IronMines/PDR2018/photo/Avancement du projet/IMG_1914.JPG

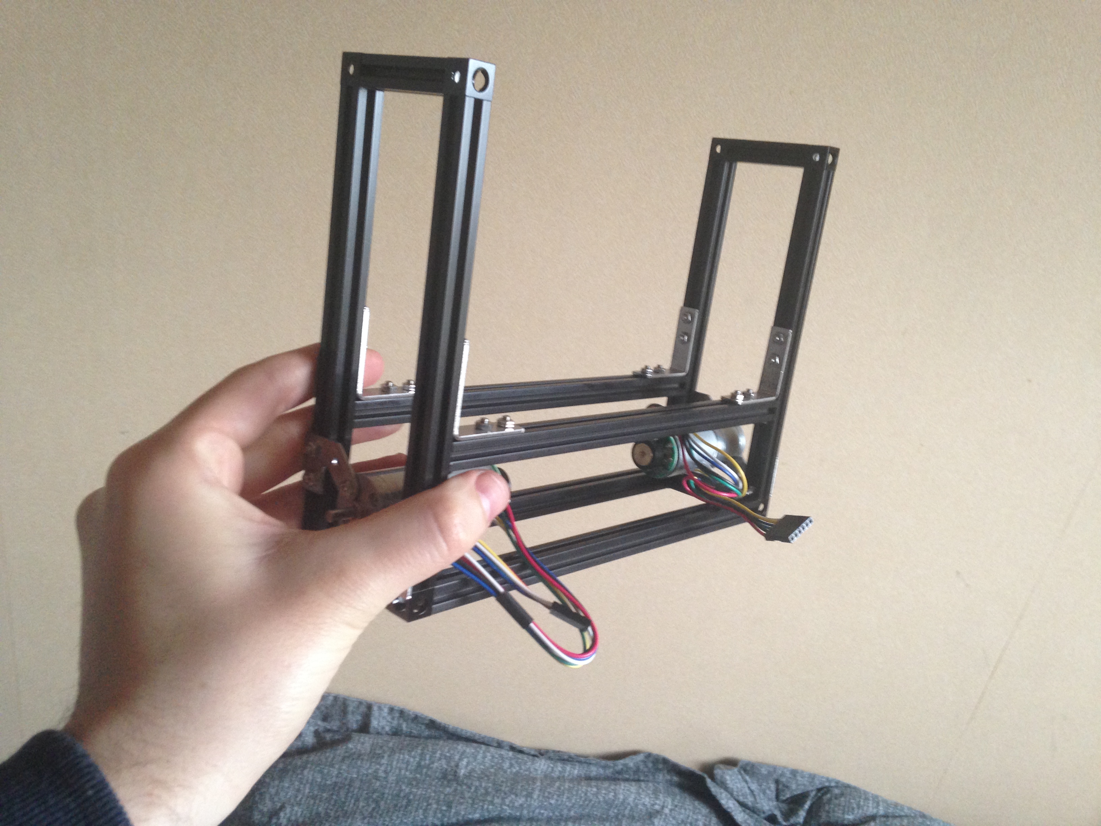
photo/Avancement du projet/IMG_1914.JPG
