IronMines/PDR2018/photo/Avancement du projet/IMG_1923.JPG

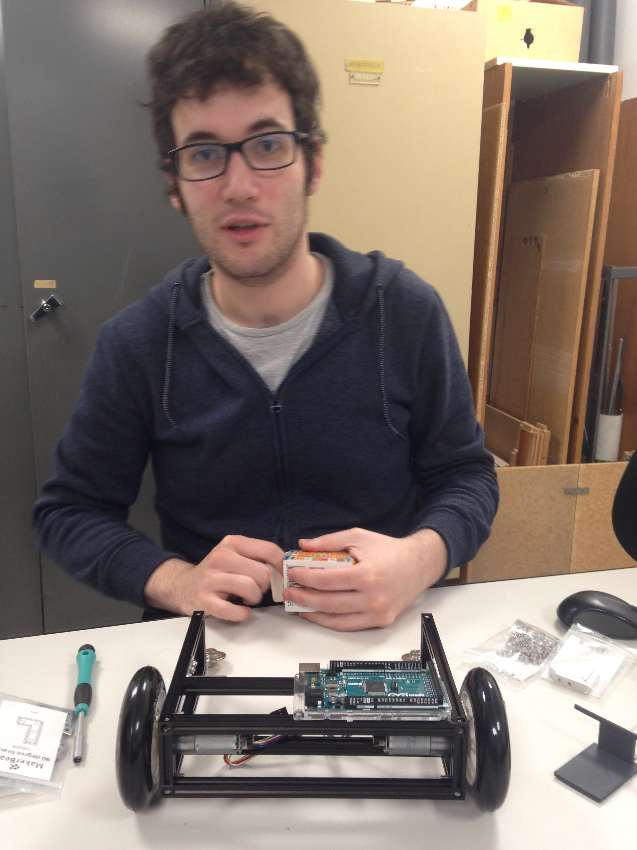
photo/Avancement du projet/IMG_1923.JPG
