IronMines/PDR2018/photo/Avancement du projet/IMG_1924.JPG

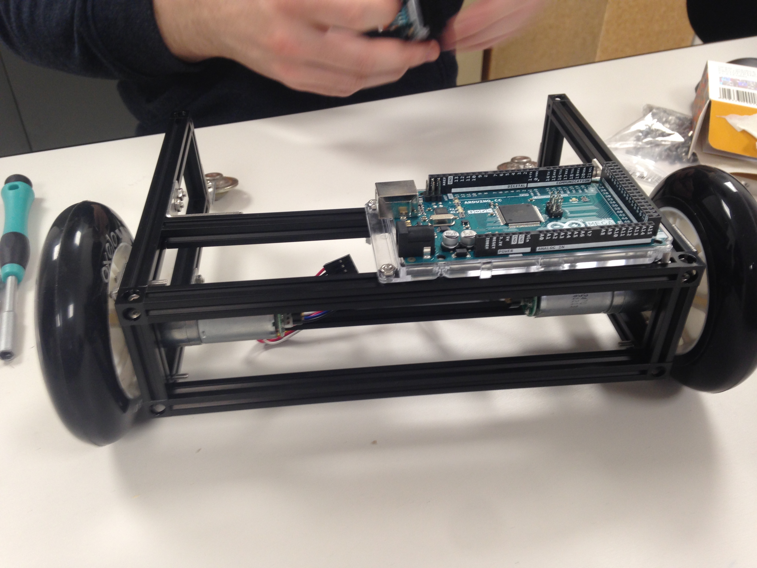
photo/Avancement du projet/IMG_1924.JPG
