IronMines/PDR2018/photo/Avancement du projet/IMG_1926.JPG

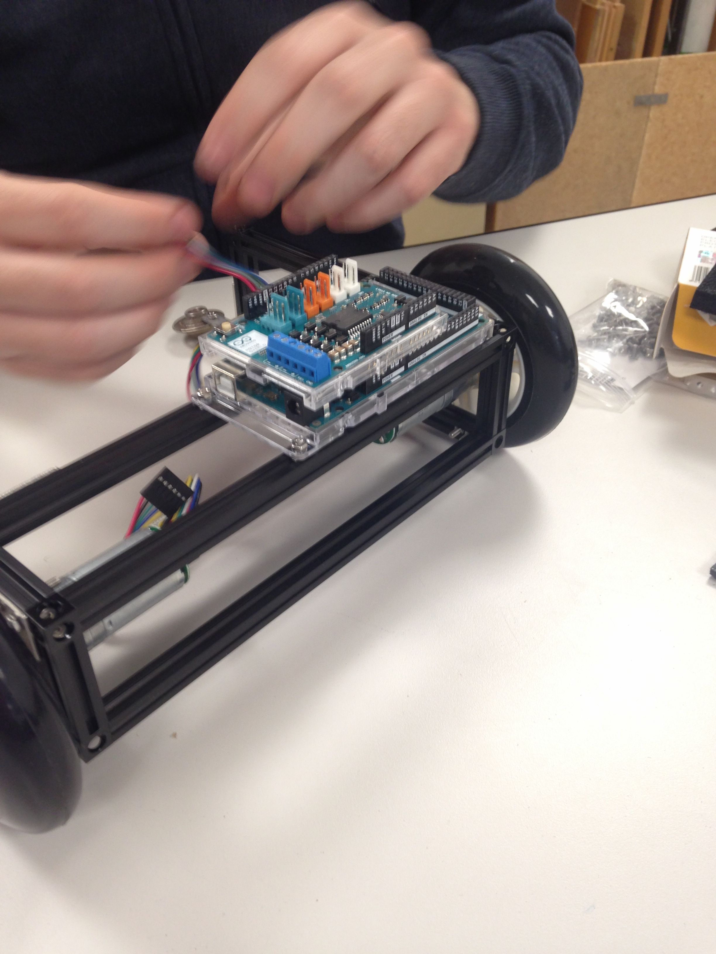
photo/Avancement du projet/IMG_1926.JPG
