IronMines/PDR2018/arduino/Sloeber/sloeber.ino.cpp

#ifdef __IN_ECLIPSE__
//This is a automatic generated file
//Please do not modify this file
//If you touch this file your change will be overwritten during the next build
//This file has been generated on 2018-05-16 20:34:54

#include "Arduino.h"
#include "Capteur.h"
#include "Moteur.h"
#include "BaseRoulante.h"
#include "StrategieDeplacement.h"
#include "GyroAndAccelerometer.h"

void setup() ;
void loop() ;
void initInterrupt() ;
void interruptAD();
void interruptAG();

#include "CodePDR.ino"


#endif
